turgu1/InkPlate-10-Extended-Case/Pictures/IMG_1441.JPG

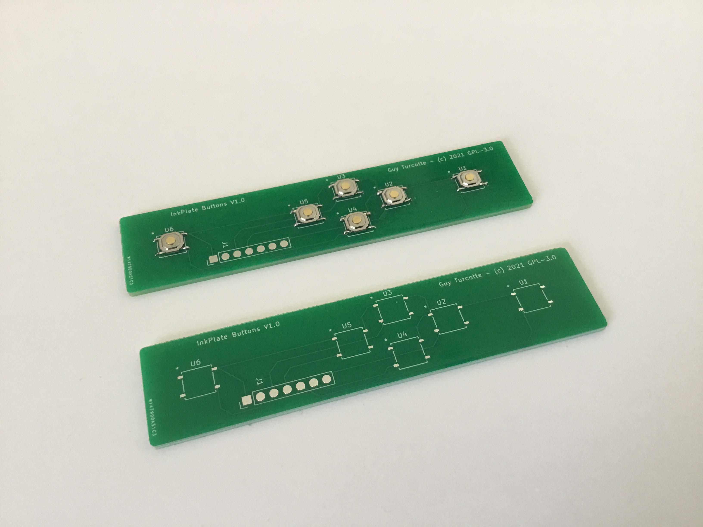
Pictures/IMG_1441.JPG
