turgu1/InkPlate-10-Extended-Case/Pictures/IMG_1447.JPG

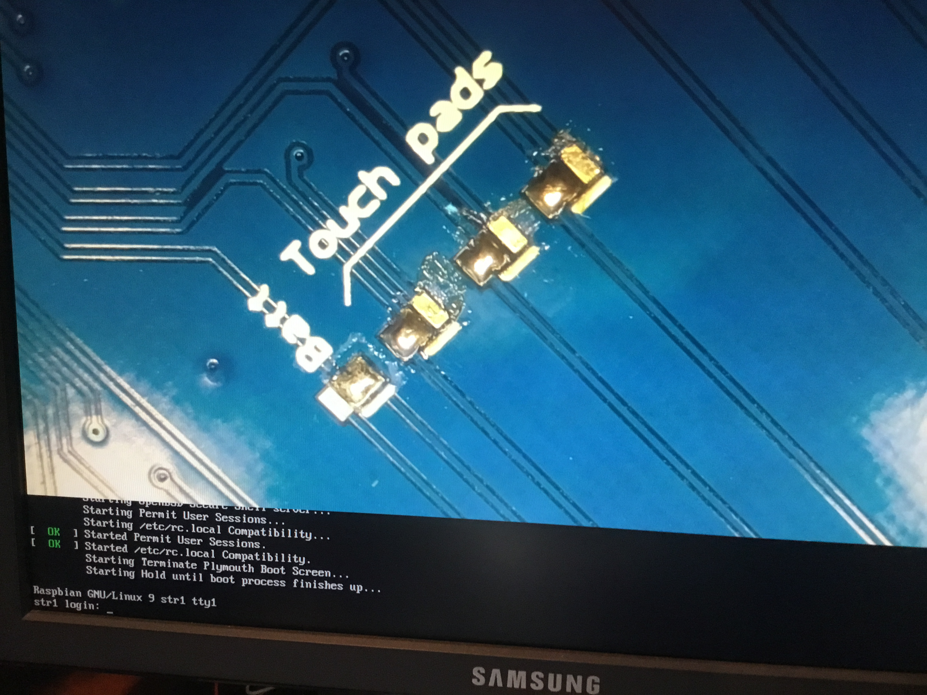
Pictures/IMG_1447.JPG
